r315/usb-cartridge/firmware/at32f415/bsp/at32f415_clock.c

#include "at32f415.h"

static volatile uint32_t ticms;

/**
  * @brief  system clock config program
  * @note   the system clock is configured as follow:
  *         system clock (sclk)   = hext / 2 * pll_mult
  *         system clock source   = pll (hext)
  *         - hext                = HEXT_VALUE
  *         - sclk                = 144000000
  *         - ahbdiv              = 1
  *         - ahbclk              = 144000000
  *         - apb2div             = 2
  *         - apb2clk             = 72000000
  *         - apb1div             = 2
  *         - apb1clk             = 72000000
  *         - pll_mult            = 36
  *         - flash_wtcyc         = 4 cycle
  * @param  none
  * @retval none
  */
void system_clock_config(void)
{
  /* reset crm */
  crm_reset();

  /* config flash psr register */
  flash_psr_set(FLASH_WAIT_CYCLE_4);

  crm_clock_source_enable(CRM_CLOCK_SOURCE_HICK, TRUE);

  /* wait till hext is ready */
  //while(crm_hext_stable_wait() == ERROR) { }

  /* config pll clock resource */
  crm_pll_config(CRM_PLL_SOURCE_HICK, CRM_PLL_MULT_36);

  /* enable pll */
  crm_clock_source_enable(CRM_CLOCK_SOURCE_PLL, TRUE);

  /* wait till pll is ready */
  while(crm_flag_get(CRM_PLL_STABLE_FLAG) != SET)
  {
  }

  /* config ahbclk */
  crm_ahb_div_set(CRM_AHB_DIV_1);

  /* config apb2clk, the maximum frequency of APB1/APB2 clock is 75 MHz  */
  crm_apb2_div_set(CRM_APB2_DIV_2);

  /* config apb1clk, the maximum frequency of APB1/APB2 clock is 75 MHz  */
  crm_apb1_div_set(CRM_APB1_DIV_2);

  /* enable auto step mode */
  crm_auto_step_mode_enable(TRUE);

  /* select pll as system clock source */
  crm_sysclk_switch(CRM_SCLK_PLL);

  /* wait till pll is used as system clock source */
  while(crm_sysclk_switch_status_get() != CRM_SCLK_PLL)
  {
  }

  /* disable auto step mode */
  crm_auto_step_mode_enable(FALSE);

  /* update system_core_clock global variable */
  system_core_clock_update();
}

/**
  * @brief  usb 48M clock select
  * @param  clk_s:USB_CLK_HICK, USB_CLK_HEXT
  * @retval none
  */
void usb_clock48m_select(usb_clk48_s clk_s)
{
  switch(system_core_clock)
  {
    /* 48MHz */
    case 48000000:
      crm_usb_clock_div_set(CRM_USB_DIV_1);
      break;

    /* 72MHz */
    case 72000000:
      crm_usb_clock_div_set(CRM_USB_DIV_1_5);
      break;

    /* 96MHz */
    case 96000000:
      crm_usb_clock_div_set(CRM_USB_DIV_2);
      break;

    /* 120MHz */
    case 120000000:
      crm_usb_clock_div_set(CRM_USB_DIV_2_5);
      break;

    /* 144MHz */
    case 144000000:
      crm_usb_clock_div_set(CRM_USB_DIV_3);
      break;

    default:
      break;

  }
}

void system_tick_init(void)
{
    SysTick_Config((system_core_clock / 1000) - 1); // config 1000us
}


/* Core Debug registers */
#define DEMCR           (*((volatile uint32_t *)0xE000EDFC))
#define DWT_CTRL        (*(volatile uint32_t *)0xe0001000)
#define CYCCNTENA       (1<<0)
#define DWT_CYCCNT      ((volatile uint32_t *)0xE0001004)
#define CPU_CYCLES      *DWT_CYCCNT
#define CLK_SPEED         168000000 // EXAMPLE for CortexM4, EDIT as needed

#define DEMCR_TRCENA    0x01000000

static uint32_t cpu_tick_us;

void cycle_count_init(void)
{
    /* Enable DWT */
    DEMCR |= DEMCR_TRCENA; 
    *DWT_CYCCNT = 0;             
    /* Enable CPU cycle counter */
    DWT_CTRL |= CYCCNTENA;

    cpu_tick_us = (SystemCoreClock / 1000000UL) + 1;
}

uint32_t get_cycle_count(void)
{
    return CPU_CYCLES;    
}

void delay_us(uint32_t us)
{
    uint32_t end_ticks = CPU_CYCLES + (us * cpu_tick_us);
    while(CPU_CYCLES < end_ticks);
}

void SysTick_Handler(void)
{ 
    ticms++;
}

void delay_ms(uint32_t ms)
{
    volatile uint32_t end = ticms + ms;
    while (ticms < end){ }
}

uint32_t get_tick(void)
{
    return ticms;
}
