r315/usb-cartridge/firmware/at32f415/app/inc/flash.h

#ifndef _flash_h_
#define _flash_h_

#include <stdint.h>

#define FLASH_CHIP_ERASE    0xFFFFFFFF

typedef enum flash_res_e{
    FLASH_OK = 0,            /* (0) Success */
    FLASH_ERROR,             /* (1) Generic error */
    FLASH_ERROR_ID,          /* (2) ID mismatch */
    FLASH_ERROR_TIMEOUT,     /* (3) Operation timedout */
}flash_res_t;

enum flash_opt_e{
    FLASH_OPT_ITF_SPI = 0,
    FLASH_OPT_ITF_NOR = 1,
    FLASH_OPT_ITF_NAND = 2,
    FLASH_OPT_ITF_MASK = 3,
    FLASH_OPT_CFI = 4
};

typedef struct {
    const char *name;
    const uint32_t size;
    const uint32_t sectorsize;
    const uint32_t pagesize;
    const uint32_t mid;             // Manufacturer/id
    const uint32_t opt;
    flash_res_t (*init)(void);
    flash_res_t (*erase)(uint32_t sector);
    flash_res_t (*read)(uint8_t *data, uint32_t addr, uint32_t len);
    flash_res_t (*write)(const uint8_t *data, uint32_t addr, uint32_t len);
    uint32_t (*id_read)(void);
}flash_t;

#endif
