r315/usb-cartridge/firmware/at32f415/app/inc/flashnor.h

#ifndef _flashnor_h_
#define _flashnor_h_

#include <stdint.h>
#include "flash.h"

#define FLASH_CMD_CFI_ADDR      0x00AA
#define FLASH_CMD_CFI_ENTER     0x98
#define FLASH_CMD_CFI_BASE_ADDR 0x0020

#define FLASH_CMD_SEQ_ADDR1     0x0555
#define FLASH_CMD_SEQ_ADDR2     0x02AA
#define FLASH_ADDR_RDMID_0      0x0000
#define FLASH_ADDR_RDMID_1      0x0001

#define FLASH_CMD_SEQ_DATA1     0xAA
#define FLASH_CMD_SEQ_DATA2     0x55

#define FLASH_CMD_RMID          0x90
#define FLASH_CMD_ERASE         0x80
#define FLASH_CMD_ERASE_CHIP    0x10
#define FLASH_CMD_ERASE_SECTOR  0x30
#define FLASH_CMD_PROGRAM       0xA0
#define FLASH_CMD_RESET         0xF0


flash_res_t flashnor_init(void);
void flashnor_deinit(void);
flash_res_t flashnor_read(uint8_t *data, uint32_t address, uint32_t len);
flash_res_t flashnor_write(const uint8_t *data, uint32_t address, uint32_t len);
uint32_t flashnor_cfi_read(uint8_t *buf);
const flash_t *flashnor_get(void);
flash_res_t flashnor_polling(uint8_t expecteddata);
uint32_t flashnor_id_read(void);
#endif
